MALITHA929/AUTOMATED-SOUND-AMPLIFIER/images/WhatsApp Image 2026-01-30 at 5.55.50 PM.jpeg

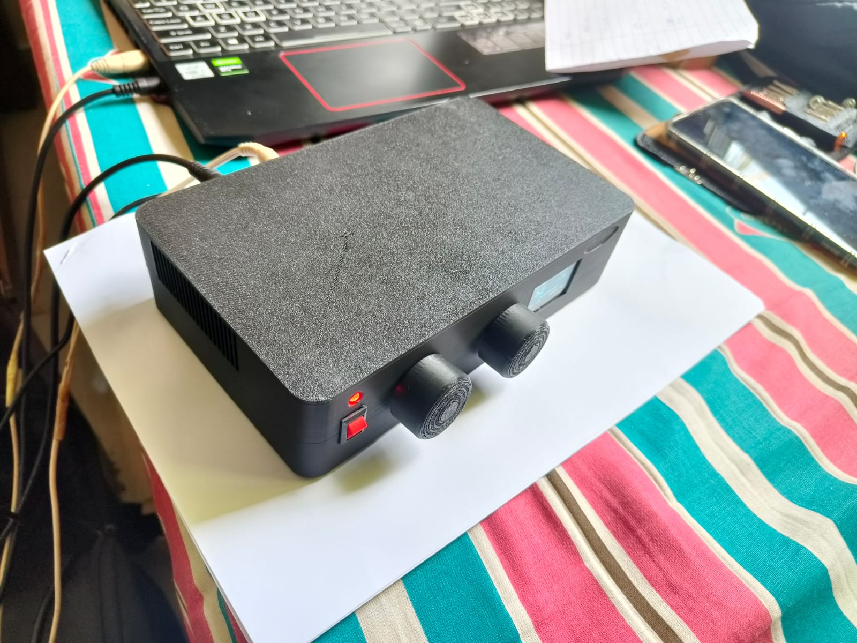
images/WhatsApp Image 2026-01-30 at 5.55.50 PM.jpeg
