MALITHA929/AUTOMATED-SOUND-AMPLIFIER/images/WhatsApp Image 2026-01-30 at 5.56.27 PM.jpeg

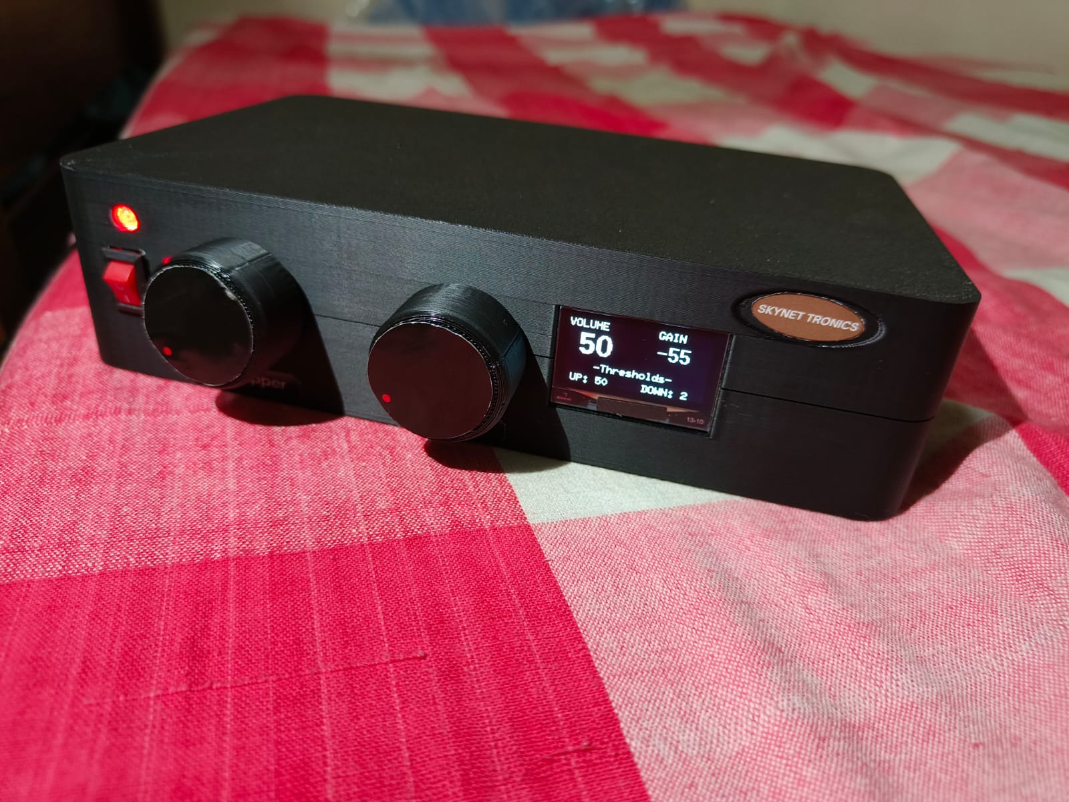
images/WhatsApp Image 2026-01-30 at 5.56.27 PM.jpeg
