MALITHA929/AUTOMATED-SOUND-AMPLIFIER/images/WhatsApp Image 2026-01-30 at 5.56.28 PM_0.jpeg

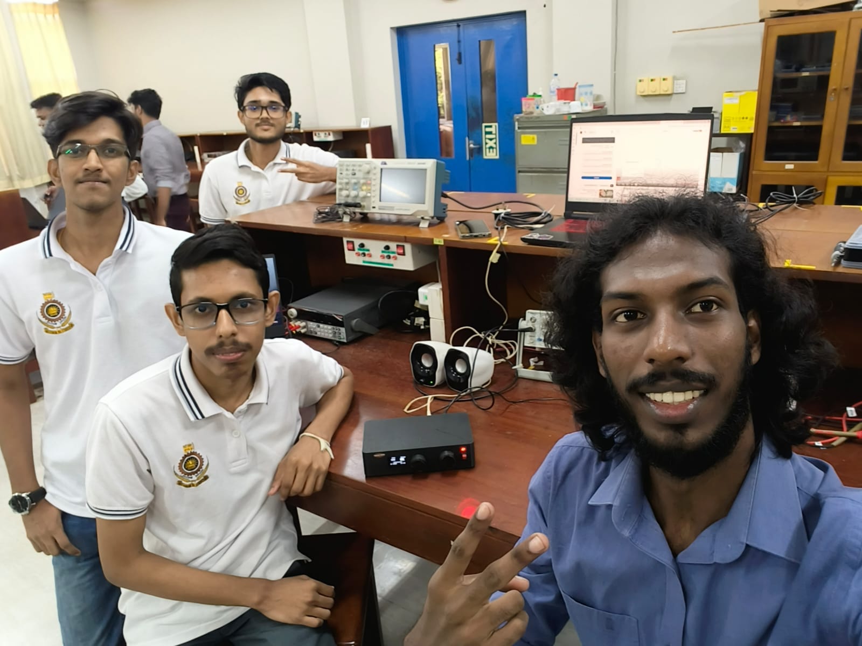
images/WhatsApp Image 2026-01-30 at 5.56.28 PM_0.jpeg
